Jorgeamin/Stokes-polarimeter/firmware/src/config/default/initialization.c

/*******************************************************************************
  System Initialization File

  File Name:
    initialization.c

  Summary:
    This file contains source code necessary to initialize the system.

  Description:
    This file contains source code necessary to initialize the system.  It
    implements the "SYS_Initialize" function, defines the configuration bits,
    and allocates any necessary global system resources,
 *******************************************************************************/

// DOM-IGNORE-BEGIN
/*******************************************************************************
* Copyright (C) 2018 Microchip Technology Inc. and its subsidiaries.
*
* Subject to your compliance with these terms, you may use Microchip software
* and any derivatives exclusively with Microchip products. It is your
* responsibility to comply with third party license terms applicable to your
* use of third party software (including open source software) that may
* accompany Microchip software.
*
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
* IN NO EVENT WILL MICROCHIP BE LIABLE FOR ANY INDIRECT, SPECIAL, PUNITIVE,
* INCIDENTAL OR CONSEQUENTIAL LOSS, DAMAGE, COST OR EXPENSE OF ANY KIND
* WHATSOEVER RELATED TO THE SOFTWARE, HOWEVER CAUSED, EVEN IF MICROCHIP HAS
* BEEN ADVISED OF THE POSSIBILITY OR THE DAMAGES ARE FORESEEABLE. TO THE
* FULLEST EXTENT ALLOWED BY LAW, MICROCHIP'S TOTAL LIABILITY ON ALL CLAIMS IN
* ANY WAY RELATED TO THIS SOFTWARE WILL NOT EXCEED THE AMOUNT OF FEES, IF ANY,
* THAT YOU HAVE PAID DIRECTLY TO MICROCHIP FOR THIS SOFTWARE.
 *******************************************************************************/
// DOM-IGNORE-END

// *****************************************************************************
// *****************************************************************************
// Section: Included Files
// *****************************************************************************
// *****************************************************************************
#include "configuration.h"
#include "definitions.h"
#include "device.h"



// ****************************************************************************
// ****************************************************************************
// Section: Configuration Bits
// ****************************************************************************
// ****************************************************************************
#pragma config NVMCTRL_BOOTPROT = 0x7
#pragma config NVMCTRL_EEPROM_SIZE = 0x7
#pragma config BOD33USERLEVEL = 0x6U
#pragma config BOD33_DIS = CLEAR
#pragma config BOD33_ACTION = 0x0
#pragma config WDT_ENABLE = CLEAR
#pragma config WDT_ALWAYSON = CLEAR
#pragma config WDT_PER = 0xB
#pragma config WDT_WINDOW = 0xB
#pragma config WDT_EWOFFSET = 0xB
#pragma config WDT_WEN = CLEAR
#pragma config BOD33_HYST = CLEAR
#pragma config NVMCTRL_REGION_LOCKS = 0xffffU




// *****************************************************************************
// *****************************************************************************
// Section: Driver Initialization Data
// *****************************************************************************
// *****************************************************************************
// <editor-fold defaultstate="collapsed" desc="DRV_I2C Instance 0 Initialization Data">

/* I2C Client Objects Pool */
static DRV_I2C_CLIENT_OBJ drvI2C0ClientObjPool[DRV_I2C_CLIENTS_NUMBER_IDX0];

/* I2C Transfer Objects Pool */
static DRV_I2C_TRANSFER_OBJ drvI2C0TransferObj[DRV_I2C_QUEUE_SIZE_IDX0];

/* I2C PLib Interface Initialization */
const DRV_I2C_PLIB_INTERFACE drvI2C0PLibAPI = {

    /* I2C PLib Transfer Read Add function */
    .read = (DRV_I2C_PLIB_READ)SERCOM0_I2C_Read,

    /* I2C PLib Transfer Write Add function */
    .write = (DRV_I2C_PLIB_WRITE)SERCOM0_I2C_Write,


    /* I2C PLib Transfer Write Read Add function */
    .writeRead = (DRV_I2C_PLIB_WRITE_READ)SERCOM0_I2C_WriteRead,

    /*I2C PLib Transfer Abort function */
    .transferAbort = (DRV_I2C_PLIB_TRANSFER_ABORT)SERCOM0_I2C_TransferAbort,

    /* I2C PLib Transfer Status function */
    .errorGet = (DRV_I2C_PLIB_ERROR_GET)SERCOM0_I2C_ErrorGet,

    /* I2C PLib Transfer Setup function */
    .transferSetup = (DRV_I2C_PLIB_TRANSFER_SETUP)SERCOM0_I2C_TransferSetup,

    /* I2C PLib Callback Register */
    .callbackRegister = (DRV_I2C_PLIB_CALLBACK_REGISTER)SERCOM0_I2C_CallbackRegister,
};


const DRV_I2C_INTERRUPT_SOURCES drvI2C0InterruptSources =
{
    /* Peripheral has single interrupt vector */
    .isSingleIntSrc                        = true,

    /* Peripheral interrupt line */
    .intSources.i2cInterrupt             = SERCOM0_IRQn,
};

/* I2C Driver Initialization Data */
const DRV_I2C_INIT drvI2C0InitData =
{
    /* I2C PLib API */
    .i2cPlib = &drvI2C0PLibAPI,

    /* I2C Number of clients */
    .numClients = DRV_I2C_CLIENTS_NUMBER_IDX0,

    /* I2C Client Objects Pool */
    .clientObjPool = (uintptr_t)&drvI2C0ClientObjPool[0],

    /* I2C TWI Queue Size */
    .transferObjPoolSize = DRV_I2C_QUEUE_SIZE_IDX0,

    /* I2C Transfer Objects */
    .transferObjPool = (uintptr_t)&drvI2C0TransferObj[0],

    /* I2C interrupt sources */
    .interruptSources = &drvI2C0InterruptSources,

    /* I2C Clock Speed */
    .clockSpeed = DRV_I2C_CLOCK_SPEED_IDX0,
};

// </editor-fold>



// *****************************************************************************
// *****************************************************************************
// Section: System Data
// *****************************************************************************
// *****************************************************************************
/* Structure to hold the object handles for the modules in the system. */
SYSTEM_OBJECTS sysObj;

// *****************************************************************************
// *****************************************************************************
// Section: Library/Stack Initialization Data
// *****************************************************************************
// *****************************************************************************
/******************************************************
 * USB Driver Initialization
 ******************************************************/
 
/*  When designing a Self-powered USB Device, the application should make sure
    that USB_DEVICE_Attach() function is called only when VBUS is actively powered.
	Therefore, the firmware needs some means to detect when the Host is powering 
	the VBUS. A 5V tolerant I/O pin can be connected to VBUS (through a resistor)
	and can be used to detect when VBUS is high or low. The application can specify
	a VBUS Detect function through the USB Driver Initialize data structure. 
	The USB device stack will periodically call this function. If the VBUS is 
	detected, the USB_DEVICE_EVENT_POWER_DETECTED event is generated. If the VBUS 
	is removed (i.e., the device is physically detached from Host), the USB stack 
	will generate the event USB_DEVICE_EVENT_POWER_REMOVED. The application should 
	call USB_DEVICE_Detach() when VBUS is removed. 
    
    The following are the steps to generate the VBUS_SENSE Function through MHC     
        1) Navigate to MHC->Tools->Pin Configuration and Configure the pin used 
		   as VBUS_SENSE. Set this pin Function as "GPIO" and set as "Input". 
		   Provide a custom name to the pin.
        2) Select the USB Driver Component in MHC Project Graph and enable the  
		   "Enable VBUS Sense" Check-box.     
        3) Specify the custom name of the VBUS SENSE pin in the "VBUS SENSE Pin Name" box.  */ 
static DRV_USB_VBUS_LEVEL DRV_USBFSV1_VBUS_Comparator(void)
{
    DRV_USB_VBUS_LEVEL retVal = DRV_USB_VBUS_LEVEL_INVALID;
    
    if(true == USB_VBUS_SENSE_Get())
    {
        retVal = DRV_USB_VBUS_LEVEL_VALID;
    }
	return (retVal);

}


const DRV_USBFSV1_INIT drvUSBInit =
{
    /* Interrupt Source for USB module */ 
    .interruptSource = USB_IRQn,

    /* System module initialization */
    .moduleInit = {0},

    /* USB Controller to operate as USB Device */
    .operationMode = DRV_USBFSV1_OPMODE_DEVICE,

    /* USB Full Speed Operation */
	.operationSpeed = USB_SPEED_FULL,
    
    /* Stop in idle */
    .runInStandby = true,

    /* Suspend in sleep */
    .suspendInSleep = false,

    /* Identifies peripheral (PLIB-level) ID */
    .usbID = USB_REGS,
	
    /* Function to check for VBus */
    .vbusComparator = DRV_USBFSV1_VBUS_Comparator
	
};




// *****************************************************************************
// *****************************************************************************
// Section: System Initialization
// *****************************************************************************
// *****************************************************************************



// *****************************************************************************
// *****************************************************************************
// Section: Local initialization functions
// *****************************************************************************
// *****************************************************************************



/*******************************************************************************
  Function:
    void SYS_Initialize ( void *data )

  Summary:
    Initializes the board, services, drivers, application and other modules.

  Remarks:
 */

void SYS_Initialize ( void* data )
{
    /* MISRAC 2012 deviation block start */
    /* MISRA C-2012 Rule 2.2 deviated in this file.  Deviation record ID -  H3_MISRAC_2012_R_2_2_DR_1 */

    NVMCTRL_REGS->NVMCTRL_CTRLB = NVMCTRL_CTRLB_RWS(3UL);

    PM_Initialize();

  
    PORT_Initialize();


    CLOCK_Initialize();




    NVMCTRL_Initialize( );

	BSP_Initialize();
    EVSYS_Initialize();

    SERCOM0_I2C_Initialize();

	SYSTICK_TimerInitialize();

    ADC_Initialize();
    TC0_TimerInitialize();


    /* Initialize I2C0 Driver Instance */
    sysObj.drvI2C0 = DRV_I2C_Initialize(DRV_I2C_INDEX_0, (SYS_MODULE_INIT *)&drvI2C0InitData);



    /* Initialize the USB device layer */
    sysObj.usbDevObject0 = USB_DEVICE_Initialize (USB_DEVICE_INDEX_0 , ( SYS_MODULE_INIT* ) & usbDevInitData);


	/* Initialize USB Driver */ 
    sysObj.drvUSBFSV1Object = DRV_USBFSV1_Initialize(DRV_USBFSV1_INDEX_0, (SYS_MODULE_INIT *) &drvUSBInit);	


    APP_USB_Initialize();
    APP_I2C_Initialize();


    NVIC_Initialize();

    /* MISRAC 2012 deviation block end */
}


/*******************************************************************************
 End of File
*/
