Jorgeamin/Stokes-polarimeter/firmware/src/config/default/peripheral/adc/plib_adc.c

/*******************************************************************************
  Analog-to-Digital Converter(ADC) PLIB

  Company
    Microchip Technology Inc.

  File Name
    plib_adc.c

  Summary
    ADC PLIB Implementation File.

  Description
    This file defines the interface to the ADC peripheral library. This
    library provides access to and control of the associated peripheral
    instance.

  Remarks:
    None.

*******************************************************************************/

// DOM-IGNORE-BEGIN
/*******************************************************************************
* Copyright (C) 2019 Microchip Technology Inc. and its subsidiaries.
*
* Subject to your compliance with these terms, you may use Microchip software
* and any derivatives exclusively with Microchip products. It is your
* responsibility to comply with third party license terms applicable to your
* use of third party software (including open source software) that may
* accompany Microchip software.
*
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
* IN NO EVENT WILL MICROCHIP BE LIABLE FOR ANY INDIRECT, SPECIAL, PUNITIVE,
* INCIDENTAL OR CONSEQUENTIAL LOSS, DAMAGE, COST OR EXPENSE OF ANY KIND
* WHATSOEVER RELATED TO THE SOFTWARE, HOWEVER CAUSED, EVEN IF MICROCHIP HAS
* BEEN ADVISED OF THE POSSIBILITY OR THE DAMAGES ARE FORESEEABLE. TO THE
* FULLEST EXTENT ALLOWED BY LAW, MICROCHIP'S TOTAL LIABILITY ON ALL CLAIMS IN
* ANY WAY RELATED TO THIS SOFTWARE WILL NOT EXCEED THE AMOUNT OF FEES, IF ANY,
* THAT YOU HAVE PAID DIRECTLY TO MICROCHIP FOR THIS SOFTWARE.
*******************************************************************************/
// DOM-IGNORE-END

// *****************************************************************************
// *****************************************************************************
// Section: Included Files
// *****************************************************************************
// *****************************************************************************
/* This section lists the other files that are included in this file.
*/

#include "interrupts.h"
#include "plib_adc.h"

// *****************************************************************************
// *****************************************************************************
// Section: Global Data
// *****************************************************************************
// *****************************************************************************

#define ADC_LINEARITY_POS  (0U)
#define ADC_LINEARITY_Msk   (0x7UL << ADC_LINEARITY_POS)

#define ADC_BIASCAL_POS  (3U)
#define ADC_BIASCAL_Msk   (0x7UL << ADC_BIASCAL_POS)

// *****************************************************************************
// *****************************************************************************
// Section: ADC Implementation
// *****************************************************************************
// *****************************************************************************

// *****************************************************************************
/* Initialize ADC module */
void ADC_Initialize( void )
{
    /* Reset ADC */
    ADC_REGS->ADC_CTRLA = (uint8_t)ADC_CTRLA_SWRST_Msk;

    while((ADC_REGS->ADC_SYNCBUSY & ADC_SYNCBUSY_SWRST_Msk) == ADC_SYNCBUSY_SWRST_Msk)
    {
        /* Wait for Synchronization */
    }
    /* Write linearity calibration in BIASREFBUF and bias calibration in BIASCOMP */
    uint32_t calib_low_word = (uint32_t)(*(uint64_t*)OTP5_ADDR);
    ADC_REGS->ADC_CALIB = (uint16_t)((ADC_CALIB_BIASREFBUF((calib_low_word & ADC_LINEARITY_Msk) >> ADC_LINEARITY_POS)) | 
                                      (ADC_CALIB_BIASCOMP((calib_low_word & ADC_BIASCAL_Msk) >> ADC_BIASCAL_POS)));

    /* Prescaler */
    ADC_REGS->ADC_CTRLB = (uint8_t)ADC_CTRLB_PRESCALER_DIV8;
    /* Sampling length */
    ADC_REGS->ADC_SAMPCTRL = (uint8_t)ADC_SAMPCTRL_SAMPLEN(2UL);

    /* Reference */
    ADC_REGS->ADC_REFCTRL = (uint8_t)ADC_REFCTRL_REFSEL_INTVCC1;

    /* Input pin */
    ADC_REGS->ADC_INPUTCTRL = (uint16_t) ADC_POSINPUT_AIN0;

    /* Resolution & Operation Mode */
    ADC_REGS->ADC_CTRLC = (uint16_t)(ADC_CTRLC_RESSEL_12BIT | ADC_CTRLC_WINMODE(0UL) );


    /* Clear all interrupt flags */
    ADC_REGS->ADC_INTFLAG = (uint8_t)ADC_INTFLAG_Msk;

    while(0U != ADC_REGS->ADC_SYNCBUSY)
    {
        /* Wait for Synchronization */
    }
}

/* Enable ADC module */
void ADC_Enable( void )
{
    ADC_REGS->ADC_CTRLA |= (uint8_t)ADC_CTRLA_ENABLE_Msk;
    while(0U != ADC_REGS->ADC_SYNCBUSY)
    {
        /* Wait for Synchronization */
    }
}

/* Disable ADC module */
void ADC_Disable( void )
{
    ADC_REGS->ADC_CTRLA &= (uint8_t)(~ADC_CTRLA_ENABLE_Msk);
    while(0U != ADC_REGS->ADC_SYNCBUSY)
    {
        /* Wait for Synchronization */
    }
}

/* Configure channel input */
void ADC_ChannelSelect( ADC_POSINPUT positiveInput, ADC_NEGINPUT negativeInput )
{
    /* Configure pin scan mode and positive and negative input pins */
    ADC_REGS->ADC_INPUTCTRL = (uint16_t) positiveInput | (uint16_t) negativeInput;

    while((ADC_REGS->ADC_SYNCBUSY & ADC_SYNCBUSY_INPUTCTRL_Msk) == ADC_SYNCBUSY_INPUTCTRL_Msk)
    {
        /* Wait for Synchronization */
    }
}

/* Start the ADC conversion by SW */
void ADC_ConversionStart( void )
{
    /* Start conversion */
    ADC_REGS->ADC_SWTRIG |= (uint8_t)ADC_SWTRIG_START_Msk;

    while((ADC_REGS->ADC_SYNCBUSY & ADC_SYNCBUSY_SWTRIG_Msk) == ADC_SYNCBUSY_SWTRIG_Msk)
    {
        /* Wait for Synchronization */
    }
}

/* Check whether auto sequence conversion is done */
bool ADC_ConversionSequenceIsFinished(void)
{
    bool seq_status = false;
    if ((ADC_REGS->ADC_SEQSTATUS & ADC_SEQSTATUS_SEQBUSY_Msk) != ADC_SEQSTATUS_SEQBUSY_Msk)
    {
        seq_status = true;
    }
    return seq_status;
}

/* Configure window comparison threshold values */
void ADC_ComparisonWindowSet(uint16_t low_threshold, uint16_t high_threshold)
{
    ADC_REGS->ADC_WINLT = low_threshold;
    ADC_REGS->ADC_WINUT = high_threshold;
    while(0U != (ADC_REGS->ADC_SYNCBUSY))
    {
        /* Wait for Synchronization */
    }
}

void ADC_WindowModeSet(ADC_WINMODE mode)
{
	ADC_REGS->ADC_CTRLC =  (ADC_REGS->ADC_CTRLC & (uint16_t)(~ADC_CTRLC_WINMODE_Msk)) | (uint16_t)((uint32_t)mode << ADC_CTRLC_WINMODE_Pos);
    while(0U != (ADC_REGS->ADC_SYNCBUSY))
    {
        /* Wait for Synchronization */
    }
}

/* Read the conversion result */
uint16_t ADC_ConversionResultGet( void )
{
    return (uint16_t)ADC_REGS->ADC_RESULT;
}

void ADC_InterruptsClear(ADC_STATUS interruptMask)
{
    ADC_REGS->ADC_INTFLAG = (uint8_t)interruptMask;
}

void ADC_InterruptsEnable(ADC_STATUS interruptMask)
{
    ADC_REGS->ADC_INTENSET = (uint8_t)interruptMask;
}

void ADC_InterruptsDisable(ADC_STATUS interruptMask)
{
    ADC_REGS->ADC_INTENCLR = (uint8_t)interruptMask;
}

/* Check whether result is ready */
bool ADC_ConversionStatusGet( void )
{
    bool status;
    status =  (((ADC_REGS->ADC_INTFLAG & ADC_INTFLAG_RESRDY_Msk) >> ADC_INTFLAG_RESRDY_Pos) != 0U);
    if (status == true)
    {
        ADC_REGS->ADC_INTFLAG = (uint8_t)ADC_INTFLAG_RESRDY_Msk;
    }
    return status;
}
